zyuu6615/26ds/03_mechanical_3d/10kg高速舵机.SLDPRT

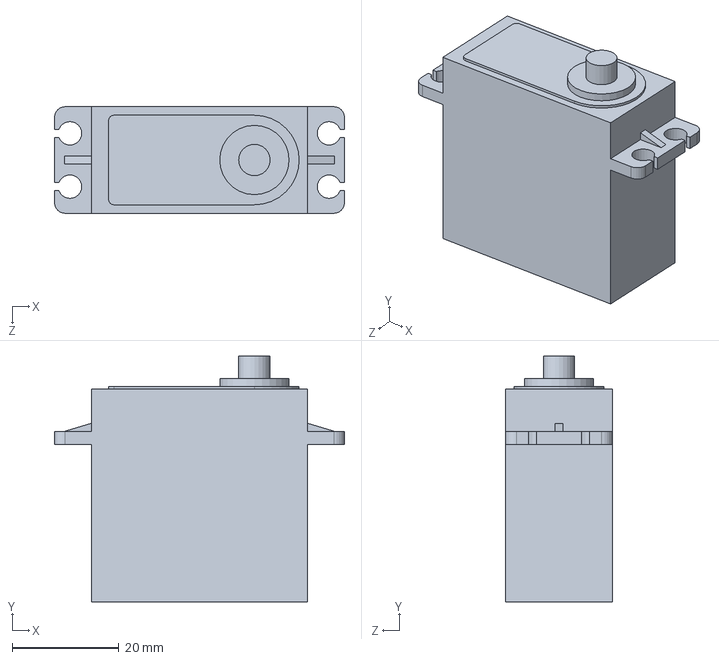
[picture p14: CAD file, 2026-09-28]
03_mechanical_3d/10kg高速舵机.SLDPRT
54.4 x 46.1 x 20.0 mm
