zyuu6615/26ds/03_mechanical_3d/合页2.SLDPRT

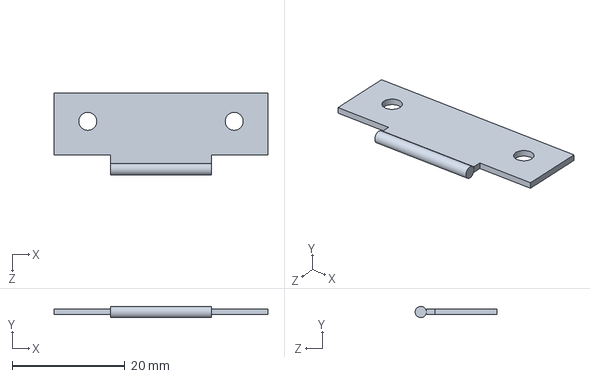
[picture p15: CAD file, 2026-09-28]
03_mechanical_3d/合页2.SLDPRT
38.0 x 2.00 x 14.5 mm
