zyuu6615/26ds/03_mechanical_3d/舵机支架.SLDPRT

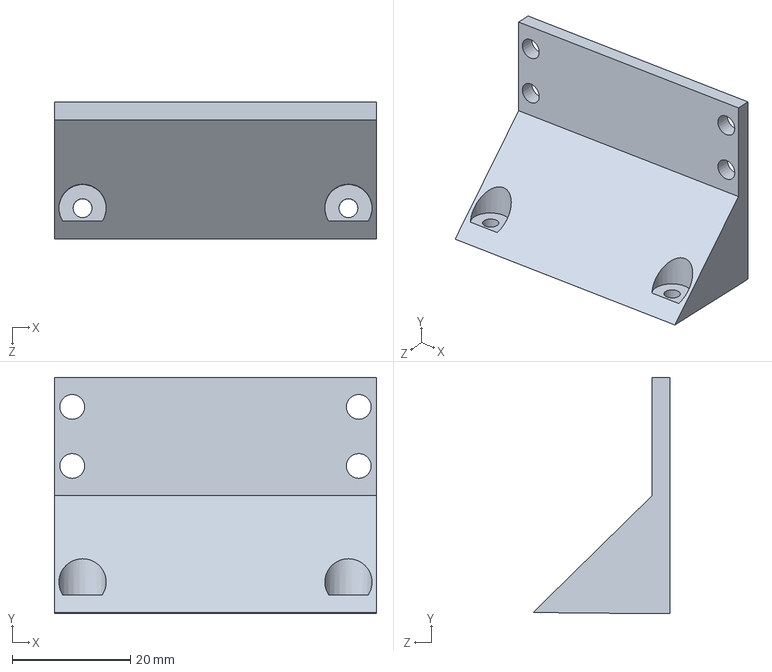
[picture p16: CAD file, 2026-09-28]
03_mechanical_3d/舵机支架.SLDPRT
54.5 x 40.0 x 23.2 mm
