zyuu6615/26ds/03_mechanical_3d/水管.SLDPRT

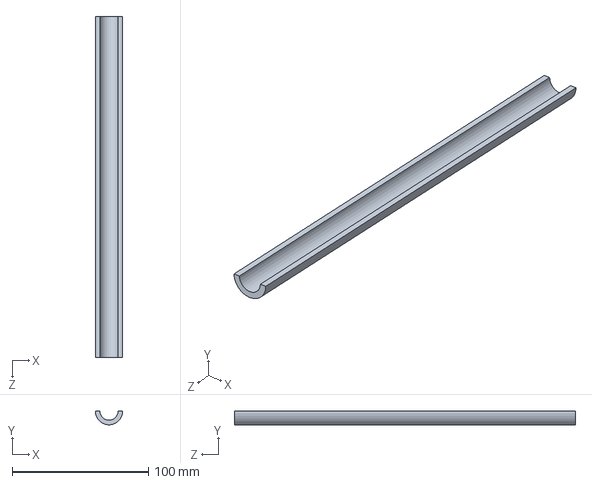
[picture p17: CAD file, 2026-09-28]
03_mechanical_3d/水管.SLDPRT
20.0 x 9.96 x 250.0 mm
