zyuu6615/26ds/01_firmware_stm32/applications/app.c

#include "app.h"
#include "lcd_spi_200.h"
#include "motor.h"
#include "encoder.h"
#include "pid.h"
#include "grayscale.h"
#include "tracking.h"
#include "key.h"
#include "task.h"
#include "servo.h"
#include "vision.h"
#include "ball.h"

#include <math.h>

/* ================= 控制参数 ================= */

/* 速度环 PID */
#define APP_PID_KP          1.5f
#define APP_PID_KI          20.0f
#define APP_PID_KD          0.0f
#define APP_PID_I_LIMIT     600.0f

/* 内环周期 10ms */
#define APP_CTRL_MS         10
#define APP_CTRL_DT         (APP_CTRL_MS / 1000.0f)

/* 外环与任务层每 2 拍跑一次 = 20ms，须与 TRACK_PERIOD_MS 一致 */
#define APP_OUTER_EVERY     (TRACK_PERIOD_MS / APP_CTRL_MS)

/* ================= 显示参数 ================= */
#define APP_FONT            ASCII_Font24       /* 字模 24(高) x 12(宽) */
#define APP_FONT_W          12

#define APP_TASK_Y          8
#define APP_STATE_Y         40
#define APP_TIME_Y          72
#define APP_GRAY_Y0         112                /* 灰度第一行 */
#define APP_GRAY_DY         28
#define APP_OFF_Y           228
#define APP_RPM_Y           258
#define APP_I2C_Y           288

#define APP_LABEL_X         14
#define APP_VALUE_X         (APP_LABEL_X + 7 * APP_FONT_W)
#define APP_VALUE_LEN       7

#define APP_GRAY_L_LABEL_X  20                 /* 左列 CH0~CH3 */
#define APP_GRAY_L_VALUE_X  (APP_GRAY_L_LABEL_X + 2 * APP_FONT_W)
#define APP_GRAY_R_LABEL_X  130                /* 右列 CH4~CH7 */
#define APP_GRAY_R_VALUE_X  (APP_GRAY_R_LABEL_X + 2 * APP_FONT_W)
#define APP_GRAY_VALUE_LEN  3

#define APP_RPM_L_X         14
#define APP_RPM_R_X         126
#define APP_RPM_VALUE_LEN   4

/* 偏差与"几路黑"共用一行 */
#define APP_OFF_VALUE_LEN   6
#define APP_DK_LABEL_X      174
#define APP_DK_VALUE_X      (APP_DK_LABEL_X + 3 * APP_FONT_W)
#define APP_DK_VALUE_LEN    2

/* ---------------- 舵机工作模式 ----------------
   四种互斥：OFF 不启动 PWM；DEMO 自动往复摆动；
   MANUAL KEY3/KEY4 步进微调(征用 KEY3，翻页失效)；BALL 球杆闭环 */
#define APP_SERVO_OFF       0
#define APP_SERVO_DEMO      1
#define APP_SERVO_MANUAL    2
#define APP_SERVO_BALL      3

#define APP_SERVO_MODE      APP_SERVO_BALL

#define APP_SERVO_ENABLE    (APP_SERVO_MODE != APP_SERVO_OFF)

/* ---------------- 分页 ----------------
   KEY3 循环切换，切页时整屏清空重画 */
typedef enum
{
  APP_PAGE_MAIN = 0,      /* 循迹主界面 */
  APP_PAGE_VISION,        /* 视觉模块原始数据 */
  APP_PAGE_BALL,          /* 球杆闭环 */
  APP_PAGE_NUM
} App_Page;

/* 刷屏走 SPI 是毫秒级阻塞操作，摊开成每次只画一个字段才不会挤占控制节拍。
   8 路灰度 + 偏差 + 黑路数 + 2 个转速 + 里程 (+ 舵机脉宽) */
#define APP_DRAW_EVERY      2
#if APP_SERVO_ENABLE
#define APP_MAIN_FIELD_NUM  (GRAY_CHANNEL_NUM + 6)
#else
#define APP_MAIN_FIELD_NUM  (GRAY_CHANNEL_NUM + 5)   /* 少一个舵机脉宽字段 */
#endif
#define APP_FIELD_OFFSET    (GRAY_CHANNEL_NUM)
#define APP_FIELD_DARK      (GRAY_CHANNEL_NUM + 1)
#define APP_FIELD_LRPM      (GRAY_CHANNEL_NUM + 2)
#define APP_FIELD_RRPM      (GRAY_CHANNEL_NUM + 3)
#define APP_FIELD_DIST      (GRAY_CHANNEL_NUM + 4)
#define APP_FIELD_SERVO     (GRAY_CHANNEL_NUM + 5)

/* ---------------- 视觉页 ---------------- */
#define APP_VIS_Y0          52
#define APP_VIS_DY          32
#define APP_VIS_VALUE_X     (APP_LABEL_X + 6 * APP_FONT_W)
#define APP_VIS_VALUE_LEN   8

enum
{
  APP_VIS_X = 0,          /* 沿摆杆轴线的位置 cm */
  APP_VIS_VX,             /* 横向像素速度 */
  APP_VIS_CONF,           /* YOLO 置信度 */
  APP_VIS_TS,             /* 视觉端时间戳 */
  APP_VIS_FRAMES,         /* 累计收到的帧数 */
  APP_VIS_ERR,            /* 解析失败 + 串口错误 */
  APP_VIS_AGE,            /* 距上一帧多久 */
  APP_VIS_LINK,           /* 链路是否新鲜 */
  APP_VISION_FIELD_NUM
};

/* ---------------- 球杆页 ---------------- */
enum
{
  APP_BALL_SET = 0,       /* 目标位置 cm */
  APP_BALL_POS,           /* 实测位置 cm */
  APP_BALL_ERR,           /* 偏差 cm */
  APP_BALL_VEL,           /* 球速 cm/s */
  APP_BALL_OUT,           /* PID 输出，相对水平点的 us 偏移 */
  APP_BALL_US,            /* 实际下发的舵机脉宽 */
  APP_BALL_STATE,         /* 是否正在闭环 */
  APP_BALL_FIELD_NUM
};

/* ERR 超过这个值就标红，取任务五/六要求的 1cm */
#define APP_BALL_ERR_LIMIT_CM   1.0f

/* 舵机脉宽显示位置，标定机构行程时直接读这个数 */
#define APP_SERVO_LABEL_X   120
#define APP_SERVO_VALUE_X   (APP_SERVO_LABEL_X + 3 * APP_FONT_W)
#define APP_SERVO_VALUE_LEN 4

/* 里程显示，用来校准轮径 */
#define APP_DIST_LABEL_X    140
#define APP_DIST_VALUE_X    (APP_DIST_LABEL_X + 2 * APP_FONT_W)
#define APP_DIST_VALUE_LEN  5

/* 计时单独刷新，不跟着字段轮转 */
#define APP_TIME_EVERY      10

/* 显示用的一阶低通系数 */
#define APP_DISP_ALPHA      0.15f

/* 实测转速低于此值(rpm)就认为车停稳，可切成短路刹车驻车 */
#define APP_STOP_RPM_TH     3.0f

/* ================= 运行时状态 ================= */
static PID_Controller s_pid[MOTOR_NUM];
static float          s_rpm[MOTOR_NUM]      = {0.0f, 0.0f};
static float          s_out[MOTOR_NUM]      = {0.0f, 0.0f};
static float          s_target[MOTOR_NUM]   = {0.0f, 0.0f};
static float          s_rpm_disp[MOTOR_NUM] = {0.0f, 0.0f};

static HAL_StatusTypeDef s_gray_status = HAL_ERROR;
static Task_ID           s_shown_task  = TASK_NUM;      /* 强制首次重画 */
static Task_State        s_shown_state = TASK_STATE_DONE;

static uint32_t s_last_tick  = 0;
static uint8_t  s_outer_cnt  = 0;
static uint8_t  s_draw_cnt   = 0;
static uint8_t  s_draw_field = 0;
static uint8_t  s_time_cnt   = 0;
static App_Page s_page       = APP_PAGE_MAIN;

/* ================= 显示：静态部分 ================= */

static uint8_t App_FieldCount(void)
{
  switch (s_page)
  {
    case APP_PAGE_VISION: return APP_VISION_FIELD_NUM;
    case APP_PAGE_BALL:   return APP_BALL_FIELD_NUM;
    default:              return APP_MAIN_FIELD_NUM;
  }
}

static void App_DrawStaticLayout(void)
{
  char label[4] = {'0', ':', '\0', '\0'};

  LCD_SetAsciiFont(&APP_FONT);
  LCD_SetColor(LCD_WHITE);

  LCD_DisplayString(APP_LABEL_X, APP_TIME_Y, "TIME:");
#if APP_SERVO_ENABLE
  LCD_DisplayString(APP_SERVO_LABEL_X, APP_STATE_Y, "US:");
#endif

  for (uint8_t i = 0; i < GRAY_CHANNEL_NUM; i++)
  {
    uint16_t x = (i < 4) ? APP_GRAY_L_LABEL_X : APP_GRAY_R_LABEL_X;
    uint16_t y = APP_GRAY_Y0 + (i % 4) * APP_GRAY_DY;

    label[0] = (char)('0' + i);
    LCD_DisplayString(x, y, label);
  }

  LCD_DisplayString(APP_LABEL_X, APP_OFF_Y, "OFF:");
  LCD_DisplayString(APP_DK_LABEL_X, APP_OFF_Y, "DK:");
  LCD_DisplayString(APP_RPM_L_X, APP_RPM_Y, "L:");
  LCD_DisplayString(APP_RPM_R_X, APP_RPM_Y, "R:");
  LCD_DisplayString(APP_LABEL_X, APP_I2C_Y, "I2C:");
  LCD_DisplayString(APP_DIST_LABEL_X, APP_I2C_Y, "D:");
}

static void App_ShowPage(void);

static void App_DrawVisionLayout(void)
{
  static const char *labels[APP_VISION_FIELD_NUM] =
  {
    "X:", "VX:", "CONF:", "TS:", "RX:", "ERR:", "AGE:", "LINK:"
  };

  LCD_SetAsciiFont(&APP_FONT);
  LCD_SetColor(LCD_WHITE);

  LCD_DisplayString((LCD_Width - 6 * APP_FONT_W) / 2, APP_TASK_Y, "VISION");

  for (uint8_t i = 0; i < APP_VISION_FIELD_NUM; i++)
  {
    LCD_DisplayString(APP_LABEL_X, APP_VIS_Y0 + i * APP_VIS_DY, (char *)labels[i]);
  }
}

static void App_DrawBallLayout(void)
{
  static const char *labels[APP_BALL_FIELD_NUM] =
  {
    "SET:", "POS:", "ERR:", "VEL:", "OUT:", "US:", "RUN:"
  };

  LCD_SetAsciiFont(&APP_FONT);
  LCD_SetColor(LCD_WHITE);

  LCD_DisplayString((LCD_Width - 4 * APP_FONT_W) / 2, APP_TASK_Y, "BALL");

  for (uint8_t i = 0; i < APP_BALL_FIELD_NUM; i++)
  {
    LCD_DisplayString(APP_LABEL_X, APP_VIS_Y0 + i * APP_VIS_DY, (char *)labels[i]);
  }
}

/* ================= 显示：字段刷新 ================= */

static void App_DrawBallField(uint8_t field)
{
  uint16_t y = APP_VIS_Y0 + field * APP_VIS_DY;

  LCD_SetAsciiFont(&APP_FONT);
  LCD_SetColor(Ball_IsTracking() ? LCD_GREEN : LCD_RED);

  switch (field)
  {
    case APP_BALL_SET:
      LCD_SetColor(LCD_WHITE);
      LCD_DisplayDecimals(APP_VIS_VALUE_X, y, Ball_GetTarget(), APP_VIS_VALUE_LEN, 2);
      break;

    case APP_BALL_POS:
      LCD_DisplayDecimals(APP_VIS_VALUE_X, y, Ball_GetPosCm(), APP_VIS_VALUE_LEN, 2);
      break;

    case APP_BALL_ERR:
    {
      float err = Ball_GetTarget() - Ball_GetPosCm();

      /* 1cm 就是任务五/六的评分门限，超了标红 —— 不用心算，扫一眼就知道达没达标 */
      LCD_SetColor((fabsf(err) > APP_BALL_ERR_LIMIT_CM) ? LCD_RED : LCD_GREEN);
      LCD_DisplayDecimals(APP_VIS_VALUE_X, y, err, APP_VIS_VALUE_LEN, 2);
      break;
    }

    case APP_BALL_VEL:
      LCD_DisplayDecimals(APP_VIS_VALUE_X, y, Ball_GetVelCmS(), APP_VIS_VALUE_LEN, 1);
      break;

    case APP_BALL_OUT:
      LCD_SetColor(LCD_CYAN);
      LCD_DisplayNumber(APP_VIS_VALUE_X, y, (int32_t)Ball_GetOutputUs(), APP_VIS_VALUE_LEN);
      break;

    case APP_BALL_US:
      LCD_SetColor(LCD_YELLOW);
      LCD_DisplayNumber(APP_VIS_VALUE_X, y, (int32_t)Servo_GetPulseUs(), APP_VIS_VALUE_LEN);
      break;

    default:    /* APP_BALL_STATE */
      LCD_DisplayString(APP_VIS_VALUE_X, y,
                        Ball_IsEnabled() ? (Ball_IsTracking() ? " TRACK " : " LOST  ")
                                         : "  OFF  ");
      break;
  }
}

static void App_DrawTaskLine(void)
{
  /* 这几行只属于主界面；在别的页上调用会画花屏幕 */
  if (s_page != APP_PAGE_MAIN)
  {
    return;
  }

  char title[8] = "TASK 1";

  LCD_SetAsciiFont(&APP_FONT);
  LCD_SetColor(LCD_WHITE);

  title[5] = (char)('1' + Task_GetId());
  LCD_DisplayString((LCD_Width - 6 * APP_FONT_W) / 2, APP_TASK_Y, title);
}

static void App_DrawStateLine(void)
{
  /* 这几行只属于主界面；在别的页上调用会画花屏幕 */
  if (s_page != APP_PAGE_MAIN)
  {
    return;
  }

  LCD_SetAsciiFont(&APP_FONT);

  switch (Task_GetState())
  {
    case TASK_STATE_RUN:
      LCD_SetColor(LCD_GREEN);
      LCD_DisplayString(APP_LABEL_X, APP_STATE_Y, "RUNNING ");
      break;

    case TASK_STATE_DONE:
      LCD_SetColor(LCD_YELLOW);
      LCD_DisplayString(APP_LABEL_X, APP_STATE_Y, "FINISHED");
      break;

    default:
      LCD_SetColor(LCD_CYAN);
      LCD_DisplayString(APP_LABEL_X, APP_STATE_Y, "READY   ");
      break;
  }
}

static void App_DrawStatus(void)
{
  /* 这几行只属于主界面；在别的页上调用会画花屏幕 */
  if (s_page != APP_PAGE_MAIN)
  {
    return;
  }

  LCD_SetAsciiFont(&APP_FONT);

  if (s_gray_status == HAL_OK)
  {
    LCD_SetColor(LCD_GREEN);
    LCD_DisplayString(APP_LABEL_X + 5 * APP_FONT_W, APP_I2C_Y, "OK  ");
  }
  else
  {
    LCD_SetColor(LCD_RED);
    LCD_DisplayString(APP_LABEL_X + 5 * APP_FONT_W, APP_I2C_Y, "FAIL");
  }
}

/* 到达评分点后改显示锁存的分段用时并标青色 */
static void App_DrawTime(void)
{
  /* 这几行只属于主界面；在别的页上调用会画花屏幕 */
  if (s_page != APP_PAGE_MAIN)
  {
    return;
  }

  uint32_t split_ms = Task_GetSplitMs();

  LCD_SetAsciiFont(&APP_FONT);

  if (split_ms != 0U)
  {
    LCD_SetColor(LCD_CYAN);
    LCD_DisplayDecimals(APP_VALUE_X, APP_TIME_Y,
                        (double)split_ms / 1000.0, APP_VALUE_LEN, 2);
    return;
  }

  LCD_SetColor(Task_IsRunning() ? LCD_WHITE : LCD_YELLOW);
  LCD_DisplayDecimals(APP_VALUE_X, APP_TIME_Y,
                      (double)Task_GetElapsedMs() / 1000.0, APP_VALUE_LEN, 2);
}

static void App_DrawVisionField(uint8_t field)
{
  const Vision_Ball *b = Vision_GetBall();
  uint16_t           y = APP_VIS_Y0 + field * APP_VIS_DY;

  LCD_SetAsciiFont(&APP_FONT);

  /* 数据过期时整页数值转灰白，避免把陈旧坐标当成实时值读 */
  LCD_SetColor(Vision_IsFresh() ? LCD_GREEN : LCD_RED);

  switch (field)
  {
    case APP_VIS_X:
      LCD_DisplayDecimals(APP_VIS_VALUE_X, y, b->x_cm, APP_VIS_VALUE_LEN, 2);
      break;

    case APP_VIS_VX:
      LCD_DisplayDecimals(APP_VIS_VALUE_X, y, b->vx_pixel_s, APP_VIS_VALUE_LEN, 1);
      break;

    case APP_VIS_CONF:
      LCD_DisplayDecimals(APP_VIS_VALUE_X, y, b->confidence, APP_VIS_VALUE_LEN, 2);
      break;

    case APP_VIS_TS:
      LCD_SetColor(LCD_WHITE);
      LCD_DisplayNumber(APP_VIS_VALUE_X, y, (int32_t)b->frame_time_ms, APP_VIS_VALUE_LEN);
      break;

    case APP_VIS_FRAMES:
      LCD_SetColor(LCD_WHITE);
      LCD_DisplayNumber(APP_VIS_VALUE_X, y, (int32_t)Vision_GetFrameCount(), APP_VIS_VALUE_LEN);
      break;

    case APP_VIS_ERR:
      /* 有错就标红。偶发几次是对端上电抖动，持续增长就是波特率或接线问题 */
      LCD_SetColor((Vision_GetErrorCount() == 0U) ? LCD_WHITE : LCD_RED);
      LCD_DisplayNumber(APP_VIS_VALUE_X, y, (int32_t)Vision_GetErrorCount(), APP_VIS_VALUE_LEN);
      break;

    case APP_VIS_AGE:
      LCD_DisplayNumber(APP_VIS_VALUE_X, y, (int32_t)Vision_GetAgeMs(), APP_VIS_VALUE_LEN);
      break;

    default:    /* APP_VIS_LINK */
      LCD_DisplayString(APP_VIS_VALUE_X, y, Vision_IsFresh() ? "  OK  " : " LOST ");
      break;
  }
}

/* 数值右对齐补空格，驱动会连背景一起重绘 */
static void App_DrawField(uint8_t field)
{
  if (s_page == APP_PAGE_VISION)
  {
    App_DrawVisionField(field);
    return;
  }
  if (s_page == APP_PAGE_BALL)
  {
    App_DrawBallField(field);
    return;
  }

  LCD_SetAsciiFont(&APP_FONT);

  if (field < GRAY_CHANNEL_NUM)
  {
    uint16_t x = (field < 4) ? APP_GRAY_L_VALUE_X : APP_GRAY_R_VALUE_X;
    uint16_t y = APP_GRAY_Y0 + (field % 4) * APP_GRAY_DY;

    LCD_SetColor(LCD_YELLOW);
    LCD_DisplayNumber(x, y, (int32_t)Track_GetRaw()[field], APP_GRAY_VALUE_LEN);
  }
  else if (field == APP_FIELD_OFFSET)
  {
    /* 压在横线上标绿、丢线标红，一眼能看出传感器当前的处境 */
    if (Track_IsCrossLine())
    {
      LCD_SetColor(LCD_GREEN);
    }
    else
    {
      LCD_SetColor(Track_IsLost() ? LCD_RED : LCD_CYAN);
    }
    LCD_DisplayDecimals(APP_VALUE_X, APP_OFF_Y, Track_GetOffset(), APP_OFF_VALUE_LEN, 1);
  }
  else if (field == APP_FIELD_DARK)
  {
    /* 有几路探头看到黑色。推着车过 A 点，看这里的峰值就能定横线阈值 */
    LCD_SetColor(Track_IsCrossLine() ? LCD_GREEN : LCD_WHITE);
    LCD_DisplayNumber(APP_DK_VALUE_X, APP_OFF_Y,
                      (int32_t)Track_GetDarkCount(), APP_DK_VALUE_LEN);
  }
  else if (field == APP_FIELD_LRPM)
  {
    LCD_SetColor(LCD_GREEN);
    LCD_DisplayNumber(APP_RPM_L_X + 2 * APP_FONT_W, APP_RPM_Y,
                      (int32_t)s_rpm_disp[MOTOR_LEFT], APP_RPM_VALUE_LEN);
  }
  else if (field == APP_FIELD_RRPM)
  {
    LCD_SetColor(LCD_GREEN);
    LCD_DisplayNumber(APP_RPM_R_X + 2 * APP_FONT_W, APP_RPM_Y,
                      (int32_t)s_rpm_disp[MOTOR_RIGHT], APP_RPM_VALUE_LEN);
  }
  else if (field == APP_FIELD_DIST)
  {
    LCD_SetColor(LCD_WHITE);
    LCD_DisplayDecimals(APP_DIST_VALUE_X, APP_I2C_Y,
                        Task_GetDistanceM(), APP_DIST_VALUE_LEN, 2);
  }
#if APP_SERVO_ENABLE
  else
  {
    LCD_SetColor(LCD_YELLOW);
    LCD_DisplayNumber(APP_SERVO_VALUE_X, APP_STATE_Y,
                      (int32_t)Servo_GetPulseUs(), APP_SERVO_VALUE_LEN);
  }
#endif
}

/* ================= 速度环（内环）================= */

static void App_SpeedLoop(void)
{
  for (uint8_t i = 0; i < MOTOR_NUM; i++)
  {
    Encoder_ID enc = (i == MOTOR_LEFT) ? ENCODER_LEFT : ENCODER_RIGHT;

    s_rpm[i] = Encoder_GetRPM(enc, APP_CTRL_MS);
    s_out[i] = PID_Update(&s_pid[i], s_target[i], s_rpm[i]);

    Motor_SetSpeed((Motor_ID)i, (int16_t)s_out[i]);

    s_rpm_disp[i] += APP_DISP_ALPHA * (s_rpm[i] - s_rpm_disp[i]);
  }
}

/* 任务未运行时：先用速度环主动反拖刹到零，停稳后再切短路刹车驻车 */
static void App_Idle(void)
{
  uint8_t moving = 0;

  for (uint8_t i = 0; i < MOTOR_NUM; i++)
  {
    Encoder_ID enc = (i == MOTOR_LEFT) ? ENCODER_LEFT : ENCODER_RIGHT;

    s_rpm[i]    = Encoder_GetRPM(enc, APP_CTRL_MS);
    s_target[i] = 0.0f;

    if (fabsf(s_rpm[i]) > APP_STOP_RPM_TH)
    {
      moving = 1;
    }

    s_rpm_disp[i] += APP_DISP_ALPHA * (s_rpm[i] - s_rpm_disp[i]);
  }

  if (moving)
  {
    /* 还在滑行：速度环主动反拖 */
    for (uint8_t i = 0; i < MOTOR_NUM; i++)
    {
      s_out[i] = PID_Update(&s_pid[i], 0.0f, s_rpm[i]);
      Motor_SetSpeed((Motor_ID)i, (int16_t)s_out[i]);
    }
    return;
  }

  /* 已经停稳：短路刹车驻车。必须清积分，否则下次启动会带着残留猛冲一下 */
  for (uint8_t i = 0; i < MOTOR_NUM; i++)
  {
    s_out[i] = 0.0f;
    PID_Reset(&s_pid[i]);
  }

  Motor_BrakeAll();
}

/* 整屏切换到当前页，之后回到每拍只刷一个字段的节奏 */
static void App_ShowPage(void)
{
  LCD_Clear();
  s_draw_field = 0;
  s_draw_cnt   = 0;

  if (s_page == APP_PAGE_VISION)
  {
    App_DrawVisionLayout();
    return;
  }
  if (s_page == APP_PAGE_BALL)
  {
    App_DrawBallLayout();
    return;
  }

  App_DrawStaticLayout();
  App_DrawTaskLine();
  App_DrawStateLine();
  App_DrawTime();
  App_DrawStatus();
}

void App_Init(void)
{
  /* ---------- LCD ---------- */
  SPI_LCD_Init();
  LCD_SetDirection(Direction_V_Flip);   /* 竖屏 240x320，整屏旋转 180 度 */
  LCD_SetBackColor(LCD_BLACK);
  LCD_SetColor(LCD_WHITE);
  LCD_Clear();
  LCD_ShowNumMode(Fill_Space);

  App_DrawStaticLayout();

  /* ---------- 视觉模块 ---------- */
  Vision_Init();

  /* ---------- 灰度传感器 ---------- */
  s_gray_status = Gray_Init();
  App_DrawStatus();

  /* ---------- 电机与编码器 ---------- */
  Motor_Init();
  Encoder_Init();

  /* ---------- 内环：两路速度 PID ---------- */
  for (uint8_t i = 0; i < MOTOR_NUM; i++)
  {
    PID_Init(&s_pid[i], APP_PID_KP, APP_PID_KI, APP_PID_KD, APP_CTRL_DT);
    PID_SetOutputLimits(&s_pid[i], -(float)MOTOR_SPEED_MAX, (float)MOTOR_SPEED_MAX);
    PID_SetIntegralLimit(&s_pid[i], APP_PID_I_LIMIT);
  }

  /* ---------- 外环与任务层 ---------- */
  Track_Init();
  Task_Init();

  /* ---------- 舵机 ---------- */
#if APP_SERVO_ENABLE
  Servo_Init();                         /* 启动 PWM，回到水平点 1500us */
#if (APP_SERVO_MODE == APP_SERVO_DEMO)
  Servo_DemoInit();
#elif (APP_SERVO_MODE == APP_SERVO_BALL)
  Ball_Init();
  Ball_Enable(1);
#endif
#endif

  /* 所有模块都初始化完了，整屏重画一次当前页 —— 与 KEY3 翻页走同一条路径，
     免得两处各画各的、以后加字段时漏掉一边 */
  App_ShowPage();
  s_shown_task  = Task_GetId();
  s_shown_state = Task_GetState();

  Motor_Enable();                       /* 解除待机，但任务未启动时是刹车状态 */

  s_last_tick = HAL_GetTick();
}

void App_Run(void)
{
  uint32_t now = HAL_GetTick();

  if ((now - s_last_tick) < APP_CTRL_MS)
  {
    return;
  }
  s_last_tick = now;

  /* ---------- 按键：每拍扫描 ---------- */
  Key_Scan();

  /* ---------- 视觉：解析中断收进来的字节 ---------- */
  Vision_Update();

#if (APP_SERVO_MODE == APP_SERVO_MANUAL)
  /* 舵机标定模式征用了 KEY3/KEY4，此时不翻页 */
#else
  /* KEY3：切换显示页面 */
  if (Key_WasPressed(KEY3))
  {
    s_page = (App_Page)((s_page + 1) % APP_PAGE_NUM);
    App_ShowPage();
  }
#endif

#if (APP_SERVO_MODE == APP_SERVO_DEMO)
  Servo_DemoUpdate();                   /* 在 1050~2400us 之间往复摆动 */
#elif (APP_SERVO_MODE == APP_SERVO_BALL)
  Ball_Update();                        /* 球杆闭环，内部只在新帧到达时动作 */
#elif (APP_SERVO_MODE == APP_SERVO_MANUAL)
  /* KEY3/KEY4：舵机以最小步进(1us)增减脉宽，用来标定机构行程。
     用 Key_WasRepeated() 而不是 Key_WasPressed()：按住会连发，
     否则 1us 一步走完整个行程要按上千下。
     KEY1/KEY2 由 Task_Update() 用 Key_WasPressed() 消费，两套事件位互不影响 */
  if (Key_WasRepeated(KEY3))
  {
    Servo_StepUs(+SERVO_STEP_US);
  }
  if (Key_WasRepeated(KEY4))
  {
    Servo_StepUs(-SERVO_STEP_US);
  }
#endif

  /* ---------- 任务层 + 循迹外环：每 2 拍 ---------- */
  s_outer_cnt++;
  if (s_outer_cnt >= APP_OUTER_EVERY)
  {
    s_outer_cnt = 0;

    /* 灰度没通就不许跑，否则会拿着全 0 的数据一头冲出去。
       静止任务(如任务三)也不能跑外环 —— 否则车会自己沿线开走 */
    if (Task_IsRunning() && Task_UsesVehicle() && (s_gray_status == HAL_OK))
    {
      HAL_StatusTypeDef status;

      Track_Update();
      Track_GetTargets(&s_target[MOTOR_LEFT], &s_target[MOTOR_RIGHT]);

      status = Track_GetStatus();
      if (status != s_gray_status)
      {
        s_gray_status = status;
        App_DrawStatus();
      }
    }
    else if (Task_IsRunning())
    {
      /* 静止任务：目标转速钉死为 0，速度环会主动把轮子按住不动 */
      s_target[MOTOR_LEFT]  = 0.0f;
      s_target[MOTOR_RIGHT] = 0.0f;
    }

    /* Task_Update 放在 Track_Update 之后，这样终点判定用的是本拍的新数据 */
    Task_Update();
  }

  /* ---------- 内环：每拍 ---------- */
  if (Task_IsRunning())
  {
    App_SpeedLoop();
  }
  else
  {
    App_Idle();
  }

  /* ---------- 显示 ---------- */
  if (Task_GetId() != s_shown_task)
  {
    s_shown_task = Task_GetId();
    App_DrawTaskLine();
  }
  if (Task_GetState() != s_shown_state)
  {
    s_shown_state = Task_GetState();
    App_DrawStateLine();
  }

  s_time_cnt++;
  if (s_time_cnt >= APP_TIME_EVERY)
  {
    s_time_cnt = 0;
    App_DrawTime();
  }

  s_draw_cnt++;
  if (s_draw_cnt >= APP_DRAW_EVERY)
  {
    s_draw_cnt = 0;
    App_DrawField(s_draw_field);
    s_draw_field = (uint8_t)((s_draw_field + 1) % App_FieldCount());
  }
}
