zyuu6615/26ds/01_firmware_stm32/applications/tracking.c

/* ================= 循迹外环 ================= */

#include "tracking.h"
#include "grayscale.h"
#include "pid.h"

#include <math.h>

/* 8 路探头安装坐标(mm)，下标 0~7 从左到右，车体中线上为 0 */
static const float s_position_mm[GRAY_CHANNEL_NUM] = TRACK_SENSOR_POSITIONS;

/* ---------------- 运行时状态 ---------------- */
static PID_Controller s_steer_pid;

static uint8_t  s_raw[GRAY_CHANNEL_NUM] = {0};
static float    s_offset      = 0.0f;      /* 最近一次的有效偏差 */
static uint8_t  s_lost        = 0;
static uint16_t s_lost_ticks  = 0;
static uint8_t  s_dark_count  = 0;         /* 有多少路探头看到黑色 */

static float    s_base_rpm    = TRACK_BASE_RPM;
static float    s_curve_slow  = TRACK_CURVE_SLOWDOWN;
static float    s_target[2]   = {0.0f, 0.0f};   /* [0]=左 [1]=右 */

static HAL_StatusTypeDef s_status = HAL_ERROR;  /* 最近一次灰度读取的结果 */

/* 加权质心：把每路的"黑度"当权重求重心，返回 1 成功、0 丢线(权重总和过小) */
static uint8_t Track_Centroid(const uint8_t *values, float *offset)
{
  float   sum_weight   = 0.0f;
  float   sum_weighted = 0.0f;
  uint8_t dark_count   = 0;

  for (uint8_t i = 0; i < GRAY_CHANNEL_NUM; i++)
  {
#if TRACK_LINE_IS_BLACK
    int32_t weight = 255 - (int32_t)values[i];
#else
    int32_t weight = (int32_t)values[i];
#endif

    if (weight >= TRACK_CROSS_WEIGHT_TH)
    {
      dark_count++;                 /* 统计有多少路是黑的 */
    }

    if (weight < TRACK_WEIGHT_NOISE_TH)
    {
      weight = 0;
    }

    sum_weight   += (float)weight;
    sum_weighted += (float)weight * s_position_mm[i];
  }

  s_dark_count = dark_count;

  if (sum_weight < (float)TRACK_LOST_TH)
  {
    return 0;                       /* 八路都没看到线 */
  }

  *offset = sum_weighted / sum_weight;
  return 1;
}

void Track_Init(void)
{
  PID_Init(&s_steer_pid, TRACK_STEER_KP, TRACK_STEER_KI, TRACK_STEER_KD,
           TRACK_PERIOD_S);
  PID_SetOutputLimits(&s_steer_pid, -TRACK_STEER_LIMIT_RPM, TRACK_STEER_LIMIT_RPM);
  PID_SetIntegralLimit(&s_steer_pid, TRACK_STEER_LIMIT_RPM / 2.0f);

  s_offset     = 0.0f;
  s_lost       = 0;
  s_lost_ticks = 0;
  s_base_rpm   = TRACK_BASE_RPM;
  s_curve_slow = TRACK_CURVE_SLOWDOWN;
  s_target[0]  = 0.0f;
  s_target[1]  = 0.0f;
}

static float Track_ClampRpm(float rpm)
{
  if (rpm > TRACK_MAX_RPM)
  {
    return TRACK_MAX_RPM;
  }
  if (rpm < -TRACK_MAX_RPM)
  {
    return -TRACK_MAX_RPM;
  }
  return rpm;
}

void Track_Update(void)
{
  uint8_t values[GRAY_CHANNEL_NUM];
  float   offset;
  float   steer;
  float   base;
  float   floor_rpm;

  /* ---------- 1. 读灰度 ---------- */
  /* I2C 失败时沿用上一次的偏差 */
  s_status = Gray_ReadAll(values);
  if (s_status == HAL_OK)
  {
    for (uint8_t i = 0; i < GRAY_CHANNEL_NUM; i++)
    {
      s_raw[i] = values[i];
    }

    /* ---------- 2. 加权质心 ---------- */
    if (Track_Centroid(values, &offset))
    {
      /* 一阶低通，抑制宽线造成的偏差跳变 */
      s_offset    += TRACK_OFFSET_LPF * (offset - s_offset);
      s_lost       = 0;
      s_lost_ticks = 0;
    }
    else
    {
      /* 丢线：偏差钉到阵列边缘之外，方向沿用丢线前 */
      s_lost = 1;
      s_offset = (s_offset >= 0.0f) ? TRACK_LOST_OFFSET_MM : -TRACK_LOST_OFFSET_MM;

      if (s_lost_ticks < 0xFFFFU)
      {
        s_lost_ticks++;
      }
    }
  }

  /* ---------- 3. 丢线超时保护 ---------- */
  if ((uint32_t)s_lost_ticks * TRACK_PERIOD_MS >= TRACK_LOST_STOP_MS)
  {
    s_target[0] = 0.0f;
    s_target[1] = 0.0f;
    return;
  }

  /* ---------- 4. 转向 PID ---------- */
  /* 目标偏差恒为 0(线压在车体中线上)；offset > 0 表示线在右侧 */
  steer = PID_Update(&s_steer_pid, 0.0f, s_offset);

  /* ---------- 5. 弯道减速 ---------- */
  /* 偏差越大减速越多 */
  base = s_base_rpm - s_curve_slow * fabsf(s_offset);

  /* 减速下限跟随基准速度 */
  floor_rpm = (s_base_rpm < TRACK_MIN_RPM) ? s_base_rpm : TRACK_MIN_RPM;
  if (base < floor_rpm)
  {
    base = floor_rpm;
  }

  s_target[0] = Track_ClampRpm(base - steer);
  s_target[1] = Track_ClampRpm(base + steer);
}

void Track_GetTargets(float *left_rpm, float *right_rpm)
{
  if (left_rpm != NULL)
  {
    *left_rpm = s_target[0];
  }
  if (right_rpm != NULL)
  {
    *right_rpm = s_target[1];
  }
}

float Track_GetOffset(void)
{
  return s_offset;
}

uint8_t Track_IsLost(void)
{
  return s_lost;
}

uint8_t Track_IsCrossLine(void)
{
  /* 多路同时黑，且车体对正 */
  return ((s_dark_count >= TRACK_CROSS_MIN_CH) &&
          (fabsf(s_offset) <= TRACK_CROSS_MAX_OFFSET_MM));
}

uint8_t Track_GetDarkCount(void)
{
  return s_dark_count;
}

const uint8_t *Track_GetRaw(void)
{
  return s_raw;
}

HAL_StatusTypeDef Track_GetStatus(void)
{
  return s_status;
}

void Track_SetBaseSpeed(float rpm)
{
  s_base_rpm = rpm;
}

void Track_SetCurveSlowdown(float rpm_per_mm)
{
  s_curve_slow = rpm_per_mm;
}

void Track_SetSteerLimit(float rpm)
{
  PID_SetOutputLimits(&s_steer_pid, -rpm, rpm);
  PID_SetIntegralLimit(&s_steer_pid, rpm / 2.0f);
}

void Track_SetTunings(float kp, float ki, float kd)
{
  PID_SetTunings(&s_steer_pid, kp, ki, kd);
}

void Track_Stop(void)
{
  s_base_rpm  = 0.0f;
  s_target[0] = 0.0f;
  s_target[1] = 0.0f;
  PID_Reset(&s_steer_pid);
}
